tylertian123/TCalc/stm/src/ptable_data.cpp

#include "ptable.hpp"

namespace pt {
	const Element PERIOD_1_ELEMENTS[] = {
		{
			"Hydrogen",
			"H",
			"1",
			"1s1",
			13.99,
			20.271,
			0.08988,
			72.769,
			1.008,
			1,
			0,
			1,
			DIATOMIC_NONMETAL,
			220,
		},
		{
			"Helium",
			"He",
			"",
			"1s2",
			0.95,
			4.222,
			0.1786,
			-48,
			4.0026022,
			2,
			2,
			18,
			NOBLE_GAS,
			0,
		},
	};

	const Element PERIOD_2_ELEMENTS[] = {
		{
			"Lithium",
			"Li",
			"1",
			"[He] 2s1",
			453.65,
			1603,
			0.534,
			59.6326,
			6.94,
			3,
			4,
			1,
			ALKALI_METAL,
			98,
		},
		{
			"Beryllium",
			"Be",
			"2",
			"[He] 2s2",
			1560,
			2742,
			1.85,
			-48,
			9.01218315,
			4,
			5,
			2,
			ALKALINE_EARTH_METAL,
			157,
		},
		{
			"Boron",
			"B",
			"3",
			"[He] 2s2 2p1",
			2349,
			4200,
			2.08,
			26.989,
			10.81,
			5,
			6,
			13,
			METALLOID,
			204,
		},
		{
			"Carbon",
			"C",
			"4",
			"[He] 2s2 2p2",
			NAN,
			NAN,
			1.821,
			121.7763,
			12.011,
			6,
			6,
			14,
			POLYATOMIC_NONMETAL,
			255,
		},
		{
			"Nitrogen",
			"N",
			"3",
			"[He] 2s2 2p3",
			63.15,
			77.355,
			1.251,
			-6.8,
			14.007,
			7,
			7,
			15,
			DIATOMIC_NONMETAL,
			304,
		},
		{
			"Oxygen",
			"O",
			"2",
			"[He] 2s2 2p4",
			54.36,
			90.188,
			1.429,
			140.976,
			15.999,
			8,
			8,
			16,
			DIATOMIC_NONMETAL,
			344,
		},
		{
			"Fluorine",
			"F",
			"1",
			"[He] 2s2 2p5",
			53.48,
			85.03,
			1.696,
			328.1649,
			18.9984031636,
			9,
			10,
			17,
			DIATOMIC_NONMETAL,
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
			"No",
			"2,3",
			"[Rn] 5f14 7s2",
			1100,
			NAN,
			NAN,
			-223.22,
			259,
			102,
			157,
			16,
			ACTINIDE,
			130,
		},
		{
			"Lawrencium",
			"Lr",
			"3",
			"[Rn] 5f14 7s2 7p1",
			1900,
			NAN,
			NAN,
			-30.04,
			266,
			103,
			163,
			17,
			ACTINIDE,
			130,
		},
	};
}
