tylertian123/TCalc/8051/include/keydef.h

#ifndef __KEYDEF_H__
#define __KEYDEF_H__

#define KEY_NULL        0x0000

#define KEY_UP          0x0001
#define KEY_DOWN        0x0002
#define KEY_LEFT        0x0003
#define KEY_RIGHT       0x0004
#define KEY_CENTER      0x0005
#define KEY_CTRL        0x0006
#define KEY_SHIFT       0x0007
#define KEY_A           0x0008
#define KEY_B           0x0009
#define KEY_C           0x000A
#define KEY_D           0x000B
#define KEY_E           0x000C
#define KEY_F           0x000D
#define KEY_G           0x000E
#define KEY_H           0x000F
#define KEY_I           0x0010
#define KEY_J           0x0011
#define KEY_K           0x0012
#define KEY_L           0x0013
#define KEY_M           0x0014
#define KEY_N           0x0015
#define KEY_O           0x0016
#define KEY_P           0x0017
#define KEY_Q           0x0018
#define KEY_R           0x0019
#define KEY_S           0x001A
#define KEY_T           0x001B
#define KEY_U           0x001C
#define KEY_V           0x001D
#define KEY_W           0x001E
#define KEY_X           0x001F
#define KEY_Y           0x0020
#define KEY_Z           0x0021
#define KEY_LCA         0x0022
#define KEY_LCB         0x0023
#define KEY_LCC         0x0024
#define KEY_LCD         0x0025
#define KEY_LCE         0x0026
#define KEY_LCF         0x0027
#define KEY_LCG         0x0028
#define KEY_LCH         0x0029
#define KEY_LCI         0x002A
#define KEY_LCJ         0x002B
#define KEY_LCK         0x002C
#define KEY_LCL         0x002D
#define KEY_LCM         0x002E
#define KEY_LCN         0x002F
#define KEY_LCO         0x0030
#define KEY_LCP         0x0031
#define KEY_LCQ         0x0032
#define KEY_LCR         0x0033
#define KEY_LCS         0x0034
#define KEY_LCT         0x0035
#define KEY_LCU         0x0036
#define KEY_LCV         0x0037
#define KEY_LCW         0x0038
#define KEY_LCX         0x0039
#define KEY_LCY         0x003A
#define KEY_LCZ         0x003B
#define KEY_0           0x003C
#define KEY_1           0x003D
#define KEY_2           0x003E
#define KEY_3           0x003F
#define KEY_4           0x0040
#define KEY_5           0x0041
#define KEY_6           0x0042
#define KEY_7           0x0043
#define KEY_8           0x0044
#define KEY_9           0x0045
#define KEY_SPACE       0x0046
#define KEY_COMMA       0x0047
#define KEY_LBRACKET    0x0048
#define KEY_RBRACKET    0x0049
#define KEY_PLUS        0x004A
#define KEY_MINUS       0x004B
#define KEY_DELETE      0x004C
#define KEY_ALLCLEAR    0x004D
#define KEY_TRIG        0x004E
#define KEY_CAT         0x004F
#define KEY_DOT         0x0050
#define KEY_MUL         0x0051
#define KEY_DIV         0x0052
#define KEY_SQUARE      0x0053
#define KEY_EXPONENT    0x0054
#define KEY_EXP         0x0055
#define KEY_LOG10       0x0056
#define KEY_EE          0x0057
#define KEY_ANS         0x0058
#define KEY_ENTER       0x0059
#define KEY_ROOT        0x005A
#define KEY_PI          0x005B
#define KEY_CONFIG      0x005C
#define KEY_SUM         0x005D
#define KEY_CLEAR       0x005E
#define KEY_PRODUCT     0x005F
#define KEY_FRAC        0x0060
#define KEY_CUBE        0x0061
#define KEY_LN          0x0062
#define KEY_LOGN        0x0063
#define KEY_APPROX      0x0064
#define KEY_NTHROOT     0x0065
#define KEY_EULER       0x0066
#define KEY_GRAPH       0x0067
#define KEY_FRACFMT     0x0068
#define KEY_EQUAL       0x0069
#define KEY_CONST       0x006A
#define KEY_CLEARVAR    0x006B
#define KEY_SHIFTON     0x006C
#define KEY_SHIFTOFF    0x006D
#define KEY_CTRLON      0x006E
#define KEY_CTRLOFF     0x006F
#define KEY_RECALL      0x0070
#define KEY_MATRIX      0x0071
#define KEY_CROSS       0x0072
#define KEY_PIECEWISE   0x0073
#define KEY_GFUNCS      0x0074
#define KEY_GSETTINGS   0x0075
#define KEY_LOGIC       0x0076
#define KEY_FACT        0x0077
#define KEY_RARROW      0x0078
#define KEY_MU          0x0079
#define KEY_SUB         0x007A
#define KEY_ABS         0x007B
#define KEY_ASTERISK    0x007C
#define KEY_AUGMENT     0x007D
#define KEY_HOME        0x007E
#define KEY_END         0x007F
#define KEY_TOP         0x0080
#define KEY_BOTTOM      0x0081
#define KEY_PTABLE      0x0082
#define KEY_VRECALL     0x0083

#define KEY_DUMMY       0xFFFF

#define KEY_ADCX_MASK   0x1000
#define KEY_ADCY_MASK   0x2000

#endif
