tylertian123/TCalc/stm/include/lcd12864.hpp

#ifndef __LCD12864_H__
#define __LCD12864_H__

#include "drawbuf.hpp"
#include "lcdbase.hpp"
#include <string.h>

namespace lcd {

    constexpr uint16_t SIZE_WIDTH = 128;
    constexpr uint16_t SIZE_HEIGHT = 64;

    class LCD12864 : public LCDBase {
    public:
        LCD12864(GPIOPin RS, GPIOPin RW, GPIOPin E, GPIOPin D0, GPIOPin D1, GPIOPin D2, GPIOPin D3, GPIOPin D4,
                GPIOPin D5, GPIOPin D6, GPIOPin D7, uint32_t timeout = 1000000)
                : LCDBase(RS, RW, E, D0, D1, D2, D3, D4, D5, D6, D7, timeout) {
        }
        LCD12864(GPIOPin RS, GPIOPin RW, GPIOPin E, GPIOPin D4, GPIOPin D5, GPIOPin D6, GPIOPin D7,
                uint32_t timeout = 1000000)
                : LCDBase(RS, RW, E, D4, D5, D6, D7, timeout) {
        }

        virtual void init() override;
        virtual void setCursor(uint8_t, uint8_t) override;
        virtual void clear() override;
        virtual void home() override;

        enum Command {
            CLEAR = 0x01, // 0000 0001
            HOME = 0x02,  // 0000 0010

            ENTRY_CURSOR_SHIFT_RIGHT = 0x06, // 0000 0110
            ENTRY_CURSOR_SHIFT_LEFT = 0x04,  // 0000 0100
            ENTRY_SCREEN_SHIFT_LEFT = 0x07,  // 0000 0111

            DISPLAY_OFF = 0x08,             // 0000 1000
            DISPLAY_ON_CURSOR_OFF = 0x0C,   // 0000 1100
            DISPLAY_ON_CURSOR_BLINK = 0x0F, // 0000 1111
            DISPLAY_ON_CURSOR_SOLID = 0x0E, // 0000 1110
            CURSOR_OFF = DISPLAY_ON_CURSOR_OFF,
            CURSOR_BLINK = DISPLAY_ON_CURSOR_BLINK,
            CURSOR_SOLID = DISPLAY_ON_CURSOR_SOLID,

            CURSOR_SHIFT_RIGHT = 0x14, // 0001 0100
            CURSOR_SHIFT_LEFT = 0x10,  // 0001 0000
            SCREEN_SHIFT_RIGHT = 0x1C, // 0001 1100
            SCREEN_SHIFT_LEFT = 0x18,  // 0001 1000

            NORMAL_CMD_8BIT = 0x30, // 0011 0000
            EXT_CMD_8BIT = 0x34,    // 0011 0100
            NORMAL_CMD_4BIT = 0x20, // 0010 0000
            EXT_CMD_4BIT = 0x24,    // 0010 0100

            EXT_STANDBY = 0x01, // 0000 0001

            EXT_ENABLE_SCROLL = 0x03, // 0000 0011
            EXT_ENABLE_RAM = 0x02,    // 0000 0010

            EXT_REVERSE_0 = 0x04, // 0000 0100
            EXT_REVERSE_1 = 0x05, // 0000 0101
            EXT_REVERSE_2 = 0x06, // 0000 0110
            EXT_REVERSE_3 = 0x07, // 0000 0111

            EXT_GRAPHICS_ON_8BIT = 0x36,  // 0011 0110
            EXT_GRAPHICS_OFF_8BIT = 0x34, // 0011 0100
            EXT_GRAPHICS_ON_4BIT = 0x26,  // 0010 0110
            EXT_GRAPHICS_OFF_4BIT = 0x24, // 0010 0100

        };

        bool isUsingExtended();
        void useExtended();
        void useBasic();

        bool isDrawing();
        void startDraw();
        void endDraw();

        void clearDrawing();
        void updateDrawing();
        void clearDrawingBuffer();
        void setPixel(int16_t, int16_t, bool state = true);
        void drawImage(int16_t, int16_t, const Image &, bool invert = false);
        void drawLine(int16_t, int16_t, int16_t, int16_t, bool invert = false);
        void drawString(int16_t, int16_t, const char *, DrawBuf::Flags flags = DrawBuf::FLAG_NONE,
                DrawBuf::Charset charset = DrawBuf::CHARSET_NORMAL);
        void fill(int16_t, int16_t, uint16_t, uint16_t, bool invert = false);
        void copyBuffer(const DrawBuf &);

        static uint16_t getDrawnStringWidth(const char *, DrawBuf::Charset charset = DrawBuf::CHARSET_NORMAL);

    protected:
        bool extendedCmd = false;
        bool drawing = false;

        // dispBuf stores what's currently being displayed
        // drawBuf is what we're working on
        // Total: 2KB of RAM
        // First index is row and second is column
        DrawBuf drawBuf;
        uint16_t dispBuf[32][16] = {0};
    };
} // namespace lcd

#endif
